jmwilson/oshw-active-probe/simulation/spice/op-amp-bandwidth.asc

C1: cap; 47p
C2: cap; {Cdm}
C3: cap; {Ccm}
C4: cap; {Cdm}
C5: cap; {Ccm}
C6: cap; 1T
C7: cap; 100p
E1: e; 1
E2: e; 0.2
L1: ind; 1T
R1: res; 66.5k
R2: res; 1.91Meg
R3: res; 10.39k
R4: res; 51k
R5: res; 5.76k
U1: OPAx140
V1: voltage; 10
V2: voltage; 10
V3: voltage; ""; AC -1
Named nets: 0, VCC, VEE, FB, OUT
.ac dec 100 1 20Meg
Aol = V(OUT)
Aol * beta = V(FB)
1/beta = V(OUT)/V(FB)
.param Ccm 7p
.param Cdm 10p
.meas AC clbw WHEN MAG(V(FB))=1
.meas AC pm FIND 180-ABS(PH(V(FB))) at clbw
.options meascplxfmt=cartesian
