jmwilson/oshw-active-probe/simulation/spice/buf802-active-probe-sparam.asc

C2: cap; 47p
C3: cap; 100p
I1: current; ""; AC 1
R6: res; 10.4k
R8: res; 20k
R9: res; 50
R10: res; 50
R11: res; 1k
R12: res; 1k
R13: res; 51k
U1: BUF802
U2: parameters
U3: OPAx140
V1: voltage; 6
V2: voltage; 6
V3: voltage; 27
V4: voltage; ""; AC 1; Rser=25
Named nets: 0, VCC, VEE, OUT, IN
.ac dec 1000 100Meg 3G
