jmwilson/oshw-active-probe/simulation/spice/buf802-active-probe.asc

C2: cap; 100p
C3: cap; 100p
C4: cap; 330p
C7: cap; 610f
I1: current; ""; AC 1
R1: res; 120
R6: res; 10.4k
R7: res; 10Meg
R8: res; 10k
R9: res; 50
R10: res; 50
R11: res; 1k
R12: res; 1k
R13: res; 51k
R15: res; 1.6Meg
R16: res; 200k
R17: res; 200k
R18: res; 976k
R19: res; 953k
R20: res; 66.5k
R21: res; 68
T1: tline; Td=95p Z0=70
T2: tline; Td=10p Z0=120
T3: tline; Td=55p Z0=120
U1: BUF802
U2: OPAx140
V1: voltage; 6
V2: voltage; 6
V3: voltage; 27
V4: voltage; ""; AC 1; Rser=25
Named nets: 0, VCC, VEE, OUT, IN
.meas AC bw WHEN mag(v(OUT))=(1/10)/sqrt(2)
.ac dec 100 1k 3G
