jmwilson/oshw-active-probe/measurement/revA/Dataset_20231117145831.csv

Name | Sweep (T1) |  | Name | Sweep (T1) |  | Name | Sweep (T1)
Date | 2023-11-17 |  | Date | 2023-11-17 |  | Date | 2023-11-17
Time | 14:57:03 |  | Time | 15:12:23 |  | Time | 15:13:12
Instrument | FPC1500 - 103124/003 |  | Instrument | FPC1500 - 103124/003 |  | Instrument | FPC1500 - 103124/003
Firmware Version | V1.80 |  | Firmware Version | V1.80 |  | Firmware Version | V1.80
Country of Origin | Czech Republic |  | Country of Origin | Czech Republic |  | Country of Origin | Czech Republic
Instrument Mode | Spectrum Analyzer |  | Instrument Mode | Spectrum Analyzer |  | Instrument Mode | Spectrum Analyzer
Meas Mode | Spectrum |  | Meas Mode | Spectrum |  | Meas Mode | Spectrum
Uplink | - - - |  | Uplink | - - - |  | Uplink | - - -
Downlink | - - - |  | Downlink | - - - |  | Downlink | - - -
Channel | - - - |  | Channel | - - - |  | Channel | - - -
Center Frequency | 1550000000 | Hz | Center Frequency | 1550000000 | Hz | Center Frequency | 1550000000 | Hz
Frequency Offset | 0 | Hz | Frequency Offset | 0 | Hz | Frequency Offset | 0 | Hz
Span | 2900000000 | Hz | Span | 2900000000 | Hz | Span | 2900000000 | Hz
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
