jmwilson/oshw-active-probe/measurement/revA/Dataset_20231117152043.csv

Name | Sweep
Date | 2023-11-17
Time | 15:19:15
Instrument | FPC1500 - 103124/003
Firmware Version | V1.80
Country of Origin | Czech Republic
Instrument Mode | Vector Network Analyzer
Meas Mode | Return Loss
Bridge Mode | S11
Format | Magnitude
Calibration State | Calibrated Interpolated
Suppression | Off
Aperture Steps | 1
Uplink | - - -
Downlink | - - -
Phase Unwrap | On
Center Frequency | 1501000000 | Hz
Frequency Offset | 0 | Hz
Span | 2998000000 | Hz
Start Frequency | 2000000 | Hz
Stop Frequency | 3000000000 | Hz
Ref Level | 0 | dB
Range | 50 | dB
Trigger Mode | Free Run
Trigger Delay | - - -
Trace Mode | Clear / Write
Trace Detector | Sample
Frequency | 0 | Hz
Number of Points | 201
Loss | 0 | dB/m
Limit Line 1 | - - -
Result Limit Line 1 | - - -
Limit Line 2 | - - -
Result Limit Line 2 | - - -
Frequency [Hz] | Magnitude [dB] | Phase [°]
2000000 | -43.032642364502 | 2.79418992996216
16990000 | -30.3869781494141 | -23.4045734405518
31980000 | -33.8488922119141 | -29.1234092712402
46970000 | -33.5272941589355 | -53.3446655273438
61960000 | -30.590087890625 | -37.7815742492676
76950000 | -30.565731048584 | -42.1603736877441
91940000 | -28.9606056213379 | -55.9176864624023
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
